kb1lqd/optical_comm_1/simulation/optical_comm_1/Receiver.asc

C1: cap; 33p
C2: cap; 9.1n
C3: cap; 1µ
I1: current; SINE(0 2u 4k 0 0 0 10)
R1: res; 10k
R2: res; 10k
R3: res; 250k
R4: res; 100k
U2: ADA4610
V1: voltage; 5V
V2: voltage; -5
Named nets: 0, Idiode, 5V, -5V
.tran 0 5m 0.1m 100u
