kb1lqd/optical_comm_1/simulation/optical_comm_1/transmitter.asc

D1: LED
M1: nmos; Si4892DY
R1: res; 1000
U1: LT118A
V1: voltage; 5
V2: voltage; 3.3
V3: voltage; PULSE(0 2 0 500u 0)
Named nets: 0, 5V, 3.3V, VCNTL
.tran 0 1m 1n 1u
