kb1lqd/optical_comm_1/simulation/led_driver.asc

C1: cap; 10µ
C2: cap; 3.9n
C3: cap; 10µ
C4: cap; 10µ
D1: LED; NSSWS108T
I1: current; 10m
R1: res; 0.1
R2: res; 100k
R3: res; 10k
R4: res; 100
R5: res; 1000Meg
R6: res; 140
R7: res; 22k
R8: res; 100k
R9: res; 10k
R10: res; 1k
R11: res; 1000Meg
R12: res; 1k
R13: res; 100k
R14: res; 1k
R15: res; 11k
R16: res; 1k
R18: res; 1k
R19: res; 1000Meg
U1: AD8648
U2: LT6106
U3: AD8648
U4: AD8648
U5: AD8648
U6: PMBF170
V1: voltage; 12
V2: voltage; SINE(4 1 4k)
V3: voltage; 5
V4: voltage; 1.2
V5: voltage; SINE(3.3 1m 1000)
Named nets: 0, 12V, 5V, VHEADPHONES, VREF, 12v, fb, inm, VMIC
;ac dec 100 1 10MEG
.tran 0 100m 1m 100u
DRIVER
HEADPHONE IN
Voltage Range
Voltage Range
MIC PRE-AMP
1-5mVp-p
0-8Vp-p
Fixed gain of 100 V/V
Variable gain of 2.4 to 12 V/V
POTENTIOMETER
OUTPUT AMP
FILTER
